f1ac0/PCMCIA-SRAM/Doc/PCMCIA_CF_Adapter.jpg

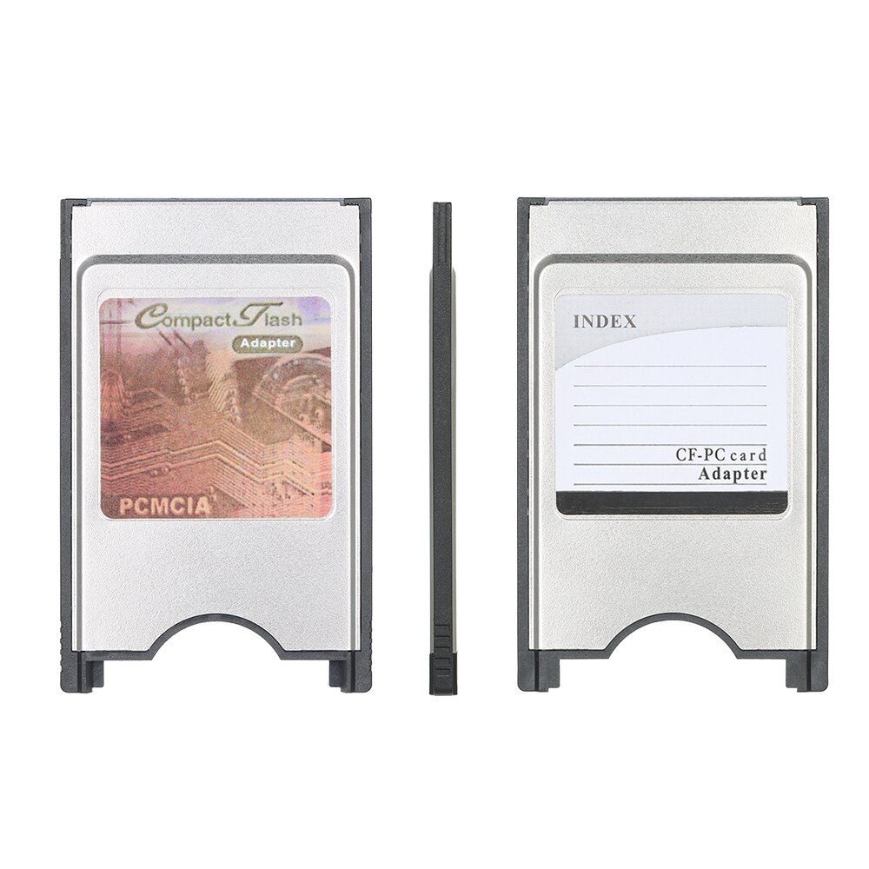
Doc/PCMCIA_CF_Adapter.jpg
