f1ac0/PCMCIA-SRAM/PCMCIA-SRAM.JPG

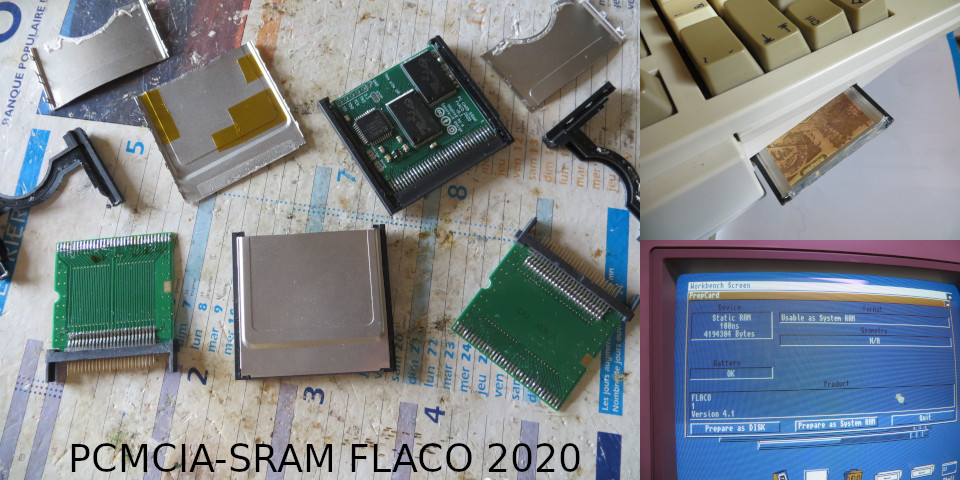
PCMCIA-SRAM.JPG
