f1ac0/PCMCIA-SRAM/Assembly process/01.The CF-PCMCIA adapter.JPG

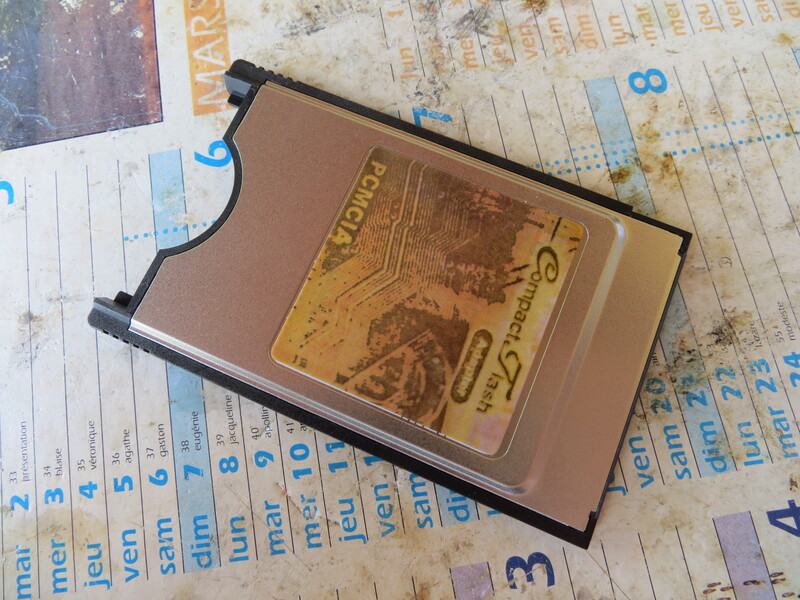
Assembly process/01.The CF-PCMCIA adapter.JPG
