f1ac0/PCMCIA-SRAM/Assembly process/06.Desoldering the PCMCIA connector.JPG

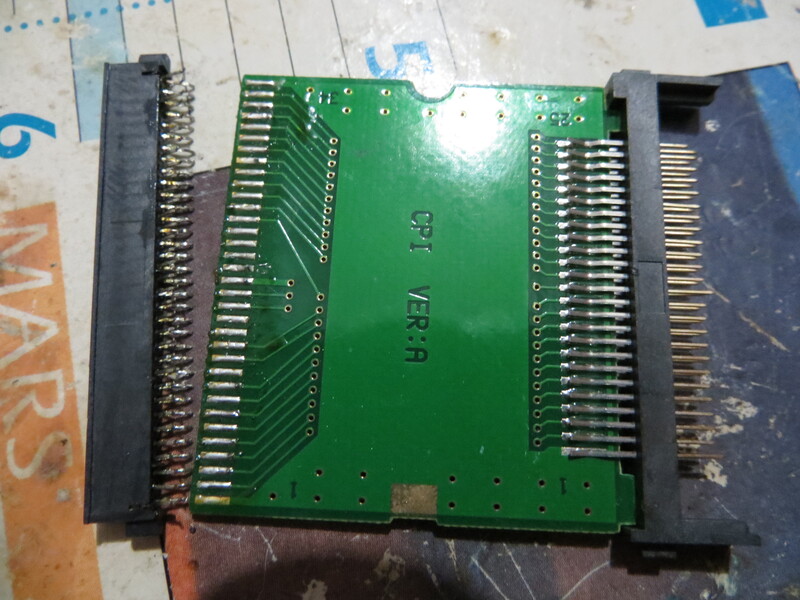
Assembly process/06.Desoldering the PCMCIA connector.JPG
