f1ac0/PCMCIA-SRAM/Assembly process/07.The PCB with SMD soldered.JPG

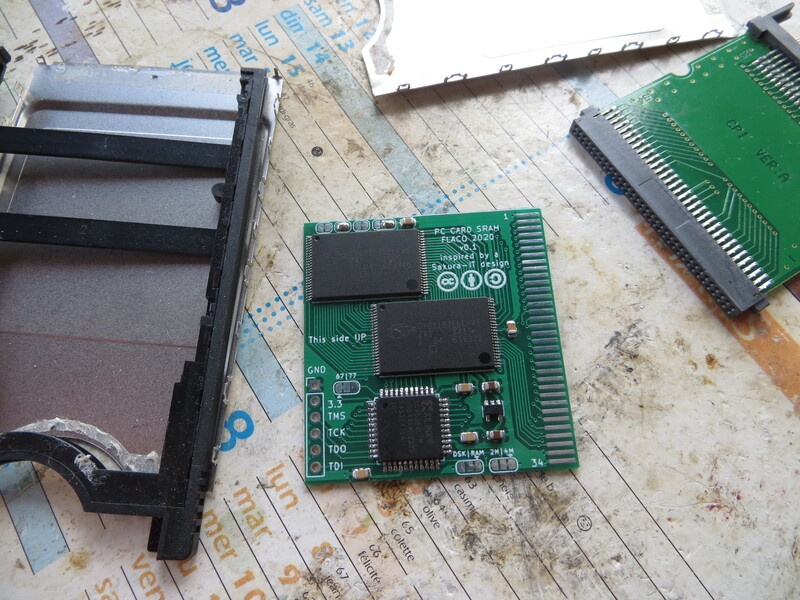
Assembly process/07.The PCB with SMD soldered.JPG
