f1ac0/PCMCIA-SRAM/Assembly process/08.The PCB with the connector.JPG

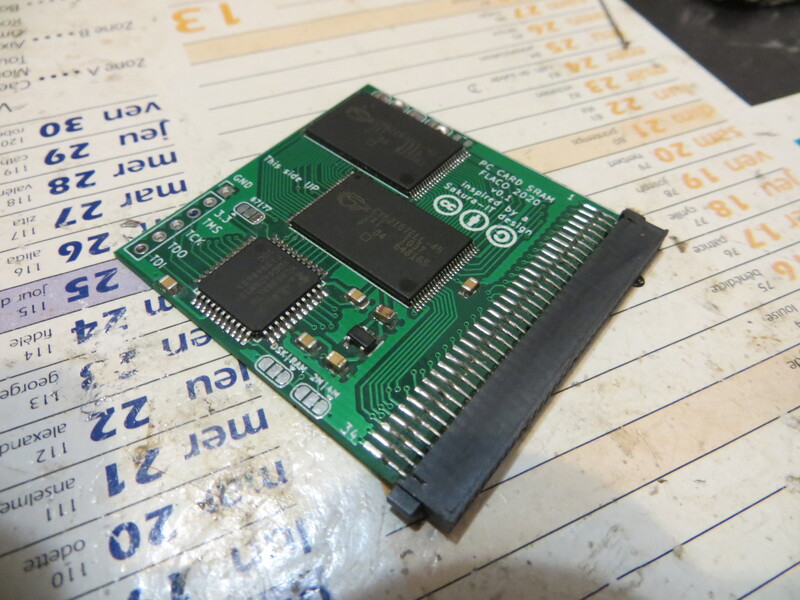
Assembly process/08.The PCB with the connector.JPG
