f1ac0/PCMCIA-SRAM/Assembly process/10.The board is detected by PrepCard.JPG

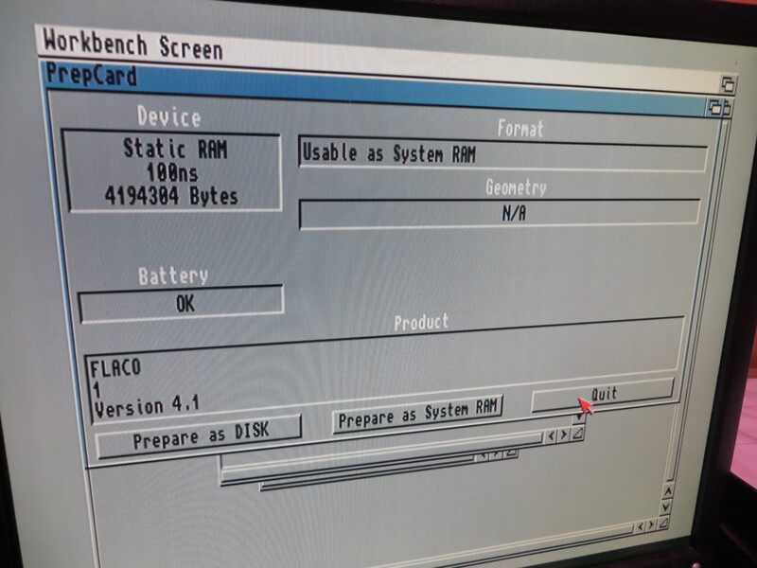
Assembly process/10.The board is detected by PrepCard.JPG
