f1ac0/PCMCIA-SRAM/Assembly process/13.Cut 1 or 2mm after the edge of the PCB.JPG

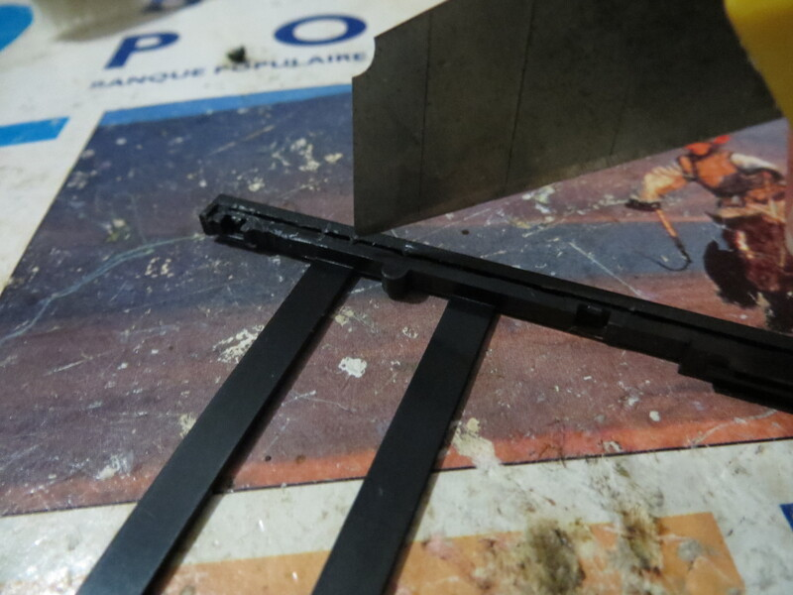
Assembly process/13.Cut 1 or 2mm after the edge of the PCB.JPG
