f1ac0/PCMCIA-SRAM/Assembly process/16.Place insulating tape just in case to prevent shorts.JPG

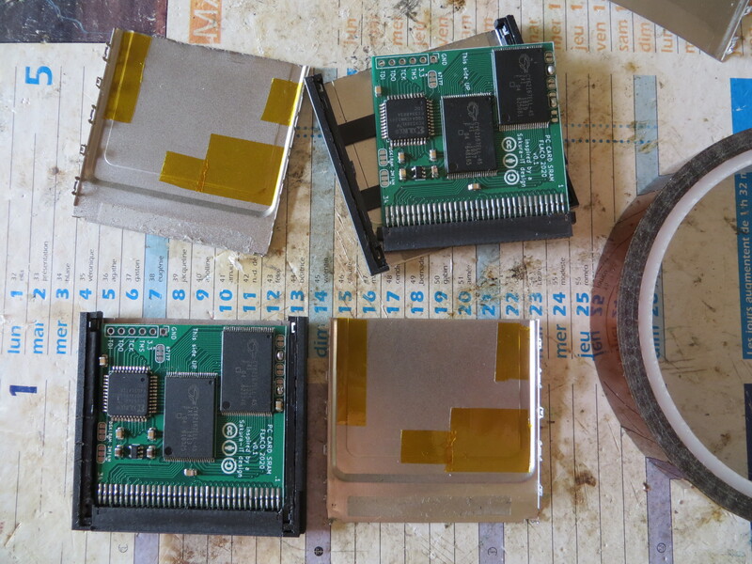
Assembly process/16.Place insulating tape just in case to prevent shorts.JPG
