f1ac0/PCMCIA-SRAM/Assembly process/17.Close the lid.JPG

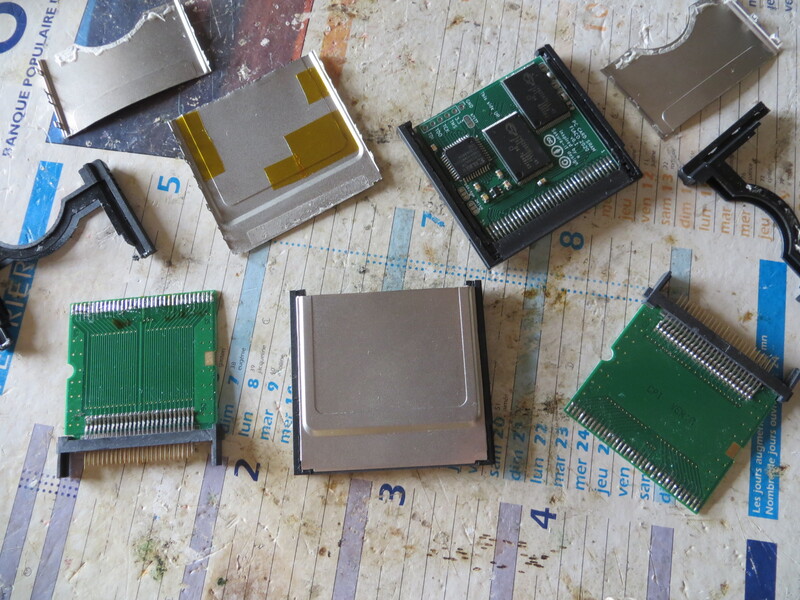
Assembly process/17.Close the lid.JPG
