f1ac0/PCMCIA-SRAM/Assembly process/18.Seal the end with hot glue or whatever.JPG

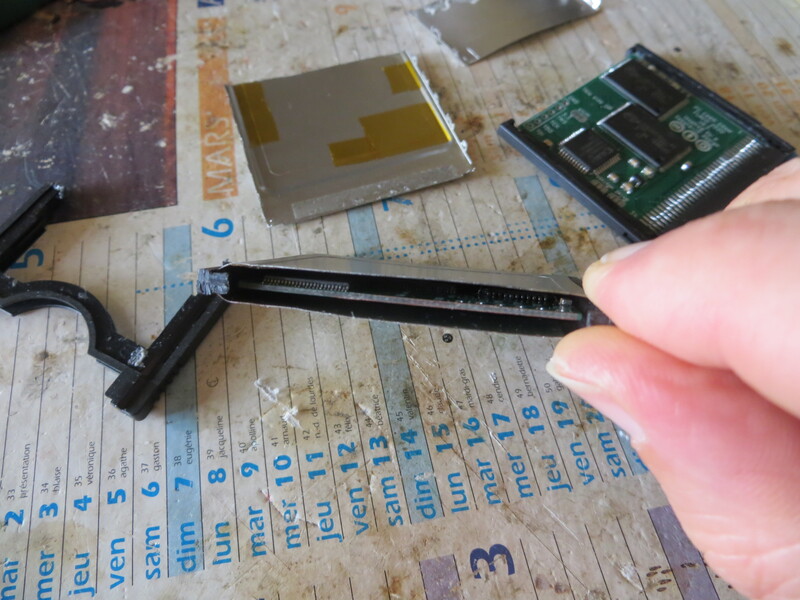
Assembly process/18.Seal the end with hot glue or whatever.JPG
