f1ac0/PCMCIA-SRAM/Assembly process/09.Testing the board.JPG

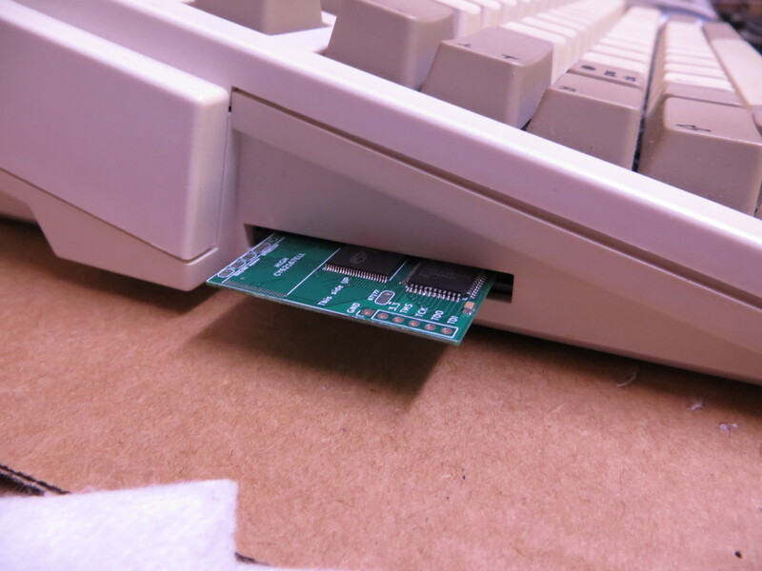
Assembly process/09.Testing the board.JPG
