f1ac0/PCMCIA-SRAM/Assembly process/12.Measure where to cut the enclosure.JPG

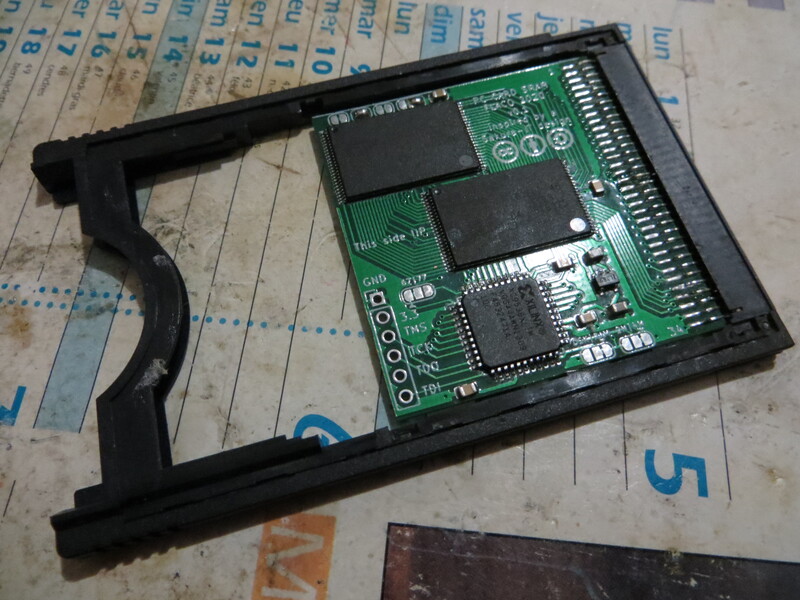
Assembly process/12.Measure where to cut the enclosure.JPG
