f1ac0/PCMCIA-SRAM/Assembly process/14.Measure where to cut the metallic covers.JPG

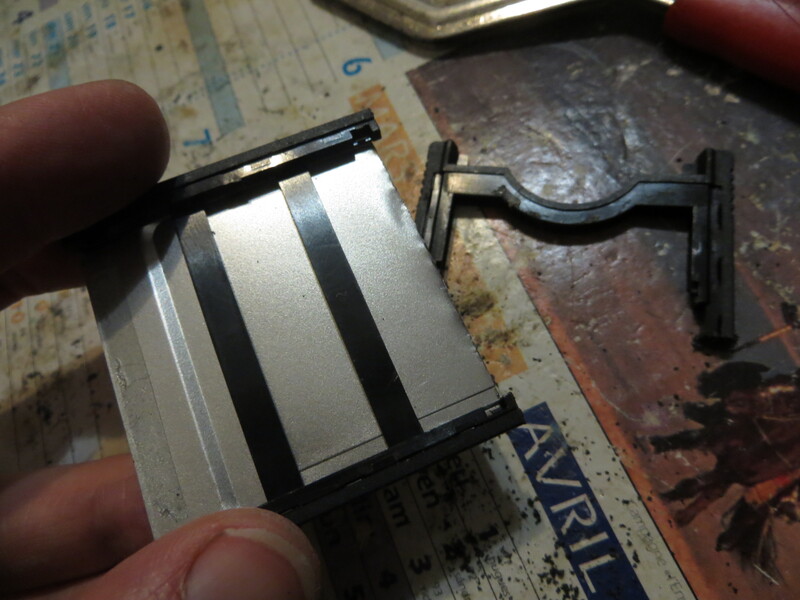
Assembly process/14.Measure where to cut the metallic covers.JPG
